attemann/Janus/RTKF3F/src/RTKF3F.cpp

#include <RTKF3F.h>

/* const char* getMessageName(MessageType type) {
    switch (type) {
    case MessageType::MSG_RTCM:            return "RTCM"; break;
    case MessageType::MSG_RTCM_FRAGMENT:   return "RTCMFRAGMENT";break;
    case MessageType::MSG_ARENA_SETTINGS:  return "FLIGHT_SETTINGS";break;
    case MessageType::MSG_GLIDER_SETTINGS: return "GLIDER_SETTINGS";break;
    case MessageType::MSG_REQ_POS:         return "REQ_POS";break;
    case MessageType::MSG_GU_GPS_SETTINGS: return "GU_GPS_SETTINGS";break;
    case MessageType::MSG_INFORMATION:     return "INFORMATION";break;
    case MessageType::MSG_ERROR:           return "ERROR";break;
    case MessageType::MSG_SIV:             return "SIV";break;
    case MessageType::MSG_G2B_EVENT:       return "G2B_EVENT";break;
    case MessageType::MSG_G2B_RELPOS:      return "G2B_RELPOS";break;
    case MessageType::MSG_G2B_MISC:        return "G2B_MISC";break;
    default:                     ;         return "UNKNOWN";break;
    }
}
*/
