attemann/Janus/GU/src/Receiver.h

// Receiver.h
#pragma once

#ifndef RECEIVER_H
#define DECEIVER_H

  #include <Arduino.h>

  // Called in setup if needed
  //void initConfigReceiver();

  // Called in loop when RFM69 has received a message
  void handleRadioMessage(uint8_t* data, uint8_t len);

  extern HardwareSerial SerialGNSS;  // Declaration only
  
  #endif
