attemann/Janus/HW_Tests/RTKBase/LCD/LCD.ino

#include <Arduino.h>
#include <LiquidCrystal_I2C.h>
#include <Wire.h>

#define LCD_SDA 4 //21
#define LCD_SCL 5 //22

LiquidCrystal_I2C lcd(0x27, 16, 2);


void setup() {

    Wire.begin(LCD_SDA, LCD_SCL);
    lcd.init();
    lcd.backlight();
    lcd.clear();

    lcd.setCursor(0,0);    lcd.print("Hei");
    lcd.setCursor(0,1);    lcd.print("Hopp");

}

void loop() {
}
